Snytbaggen/toasty-arcade-machine/godot/games/dodge/lisse/lisse.png

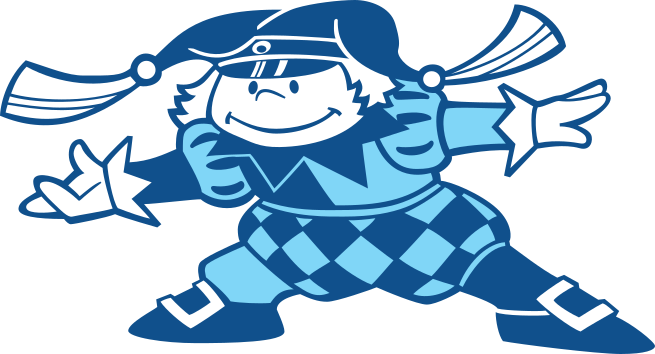
godot/games/dodge/lisse/lisse.png
