Snytbaggen/toasty-arcade-machine/godot/games/flappy_bird/res/sprites/score_bg.png

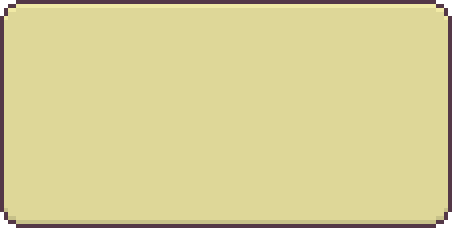
godot/games/flappy_bird/res/sprites/score_bg.png
