Snytbaggen/toasty-arcade-machine/godot/graphics/hype_bg.png

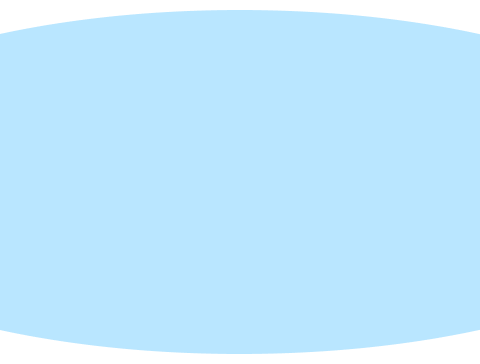
godot/graphics/hype_bg.png
